so1der/zero-node/zero-node-kicad/1888725-4280554912.png

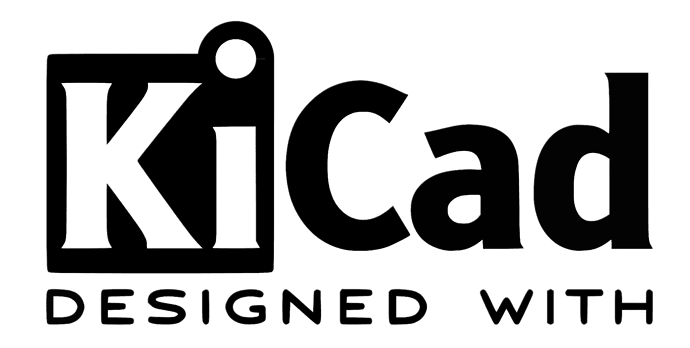
zero-node-kicad/1888725-4280554912.png
